afathouse/ECE8803_HomeworkX/Plot/Gain_4.png

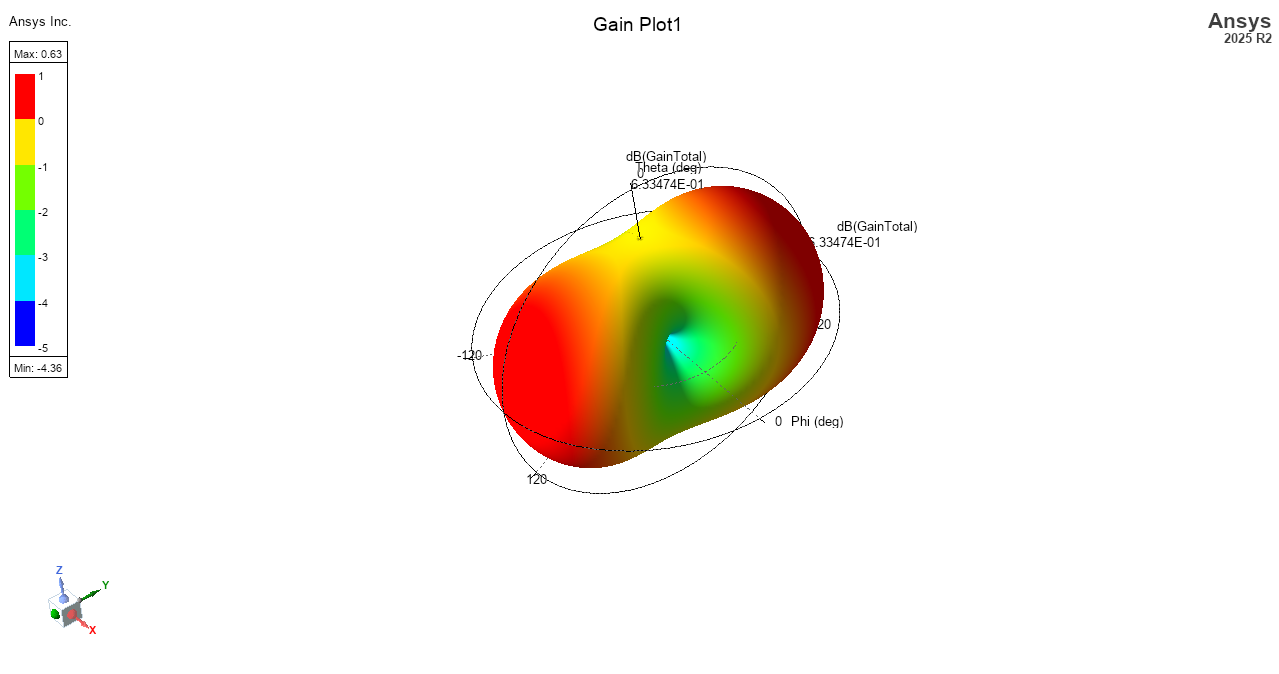
Plot/Gain_4.png
