afathouse/ECE8803_HomeworkX/Plot/Terminal S_Parameter_8.png

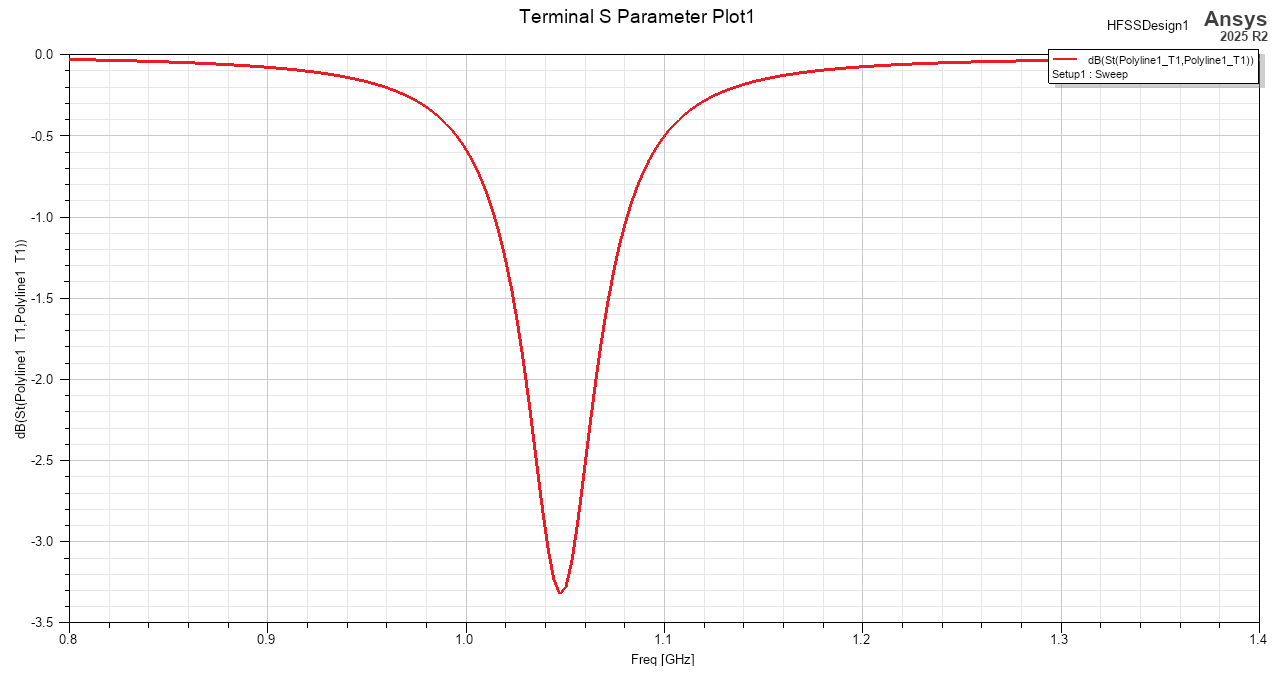
Plot/Terminal S_Parameter_8.png
