afathouse/ECE8803_HomeworkX/Plot/Terminal Z_Parameter_8.png

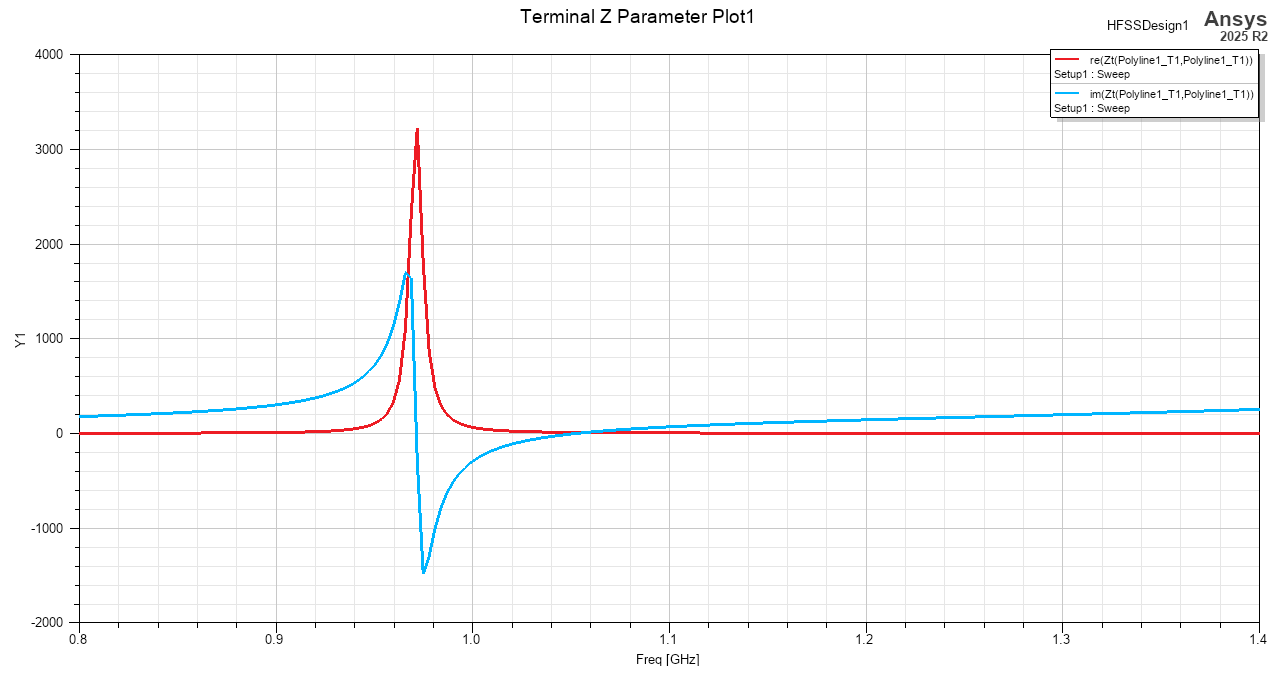
Plot/Terminal Z_Parameter_8.png
